patrickjane/arduino-wifi-temperature/icons.h

static const unsigned char PROGMEM wifi1_icon16x16[] =
{
        0b00000000, 0b00000000,
        0b00000000, 0b00000000,
        0b00000000, 0b00000000,
        0b00000000, 0b00000000,
        0b00000000, 0b00000000,
        0b00000000, 0b00000000,
        0b00000000, 0b00000000,
        0b00000000, 0b00000000,
        0b00000011, 0b11000000,
        0b00000111, 0b11100000,
        0b00000100, 0b00100000,
        0b00000001, 0b10000000,
        0b00000001, 0b10000000,
        0b00000000, 0b00000000,
        0b00000000, 0b00000000,
        0b00000000, 0b00000000,
};

static const unsigned char PROGMEM wifi2_icon16x16[] =
{
        0b00000000, 0b00000000,
        0b00000000, 0b00000000,
        0b00000000, 0b00000000,
        0b00000000, 0b00000000,
        0b00000000, 0b00000000,
        0b00000111, 0b11100000,
        0b00001111, 0b11110000,
        0b00011000, 0b00011000,
        0b00000011, 0b11000000,
        0b00000111, 0b11100000,
        0b00000100, 0b00100000,
        0b00000001, 0b10000000,
        0b00000001, 0b10000000,
        0b00000000, 0b00000000,
        0b00000000, 0b00000000,
        0b00000000, 0b00000000,
};

static const unsigned char PROGMEM wifi3_icon16x16[] =
{
        0b00000000, 0b00000000,
        0b00000111, 0b11100000,
        0b00011111, 0b11111000,
        0b00111111, 0b11111100,
        0b01110000, 0b00001110,
        0b01100111, 0b11100110,
        0b00001111, 0b11110000,
        0b00011000, 0b00011000,
        0b00000011, 0b11000000,
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
        0b00000111,0b11000000,
        0b00001111,0b11100000,
        0b00001111,0b11100000,
        0b00001111,0b11100000,
        0b00000111,0b11000000,
        0b00000011,0b10000000,
        0b00000000,0b00000000,
        0b00000000,0b00000000,
        0b00000000,0b00000000,
};
